evaEko/knife_whetting_level/docs/images/pcb_assembly/01-assembly_buttons.jpg

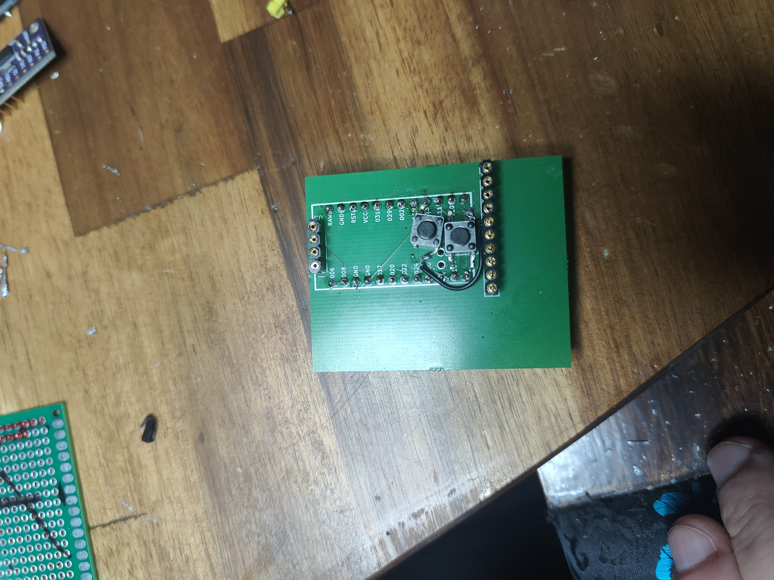
docs/images/pcb_assembly/01-assembly_buttons.jpg
