evaEko/knife_whetting_level/docs/images/pcb_assembly/02-assembly_display.jpg

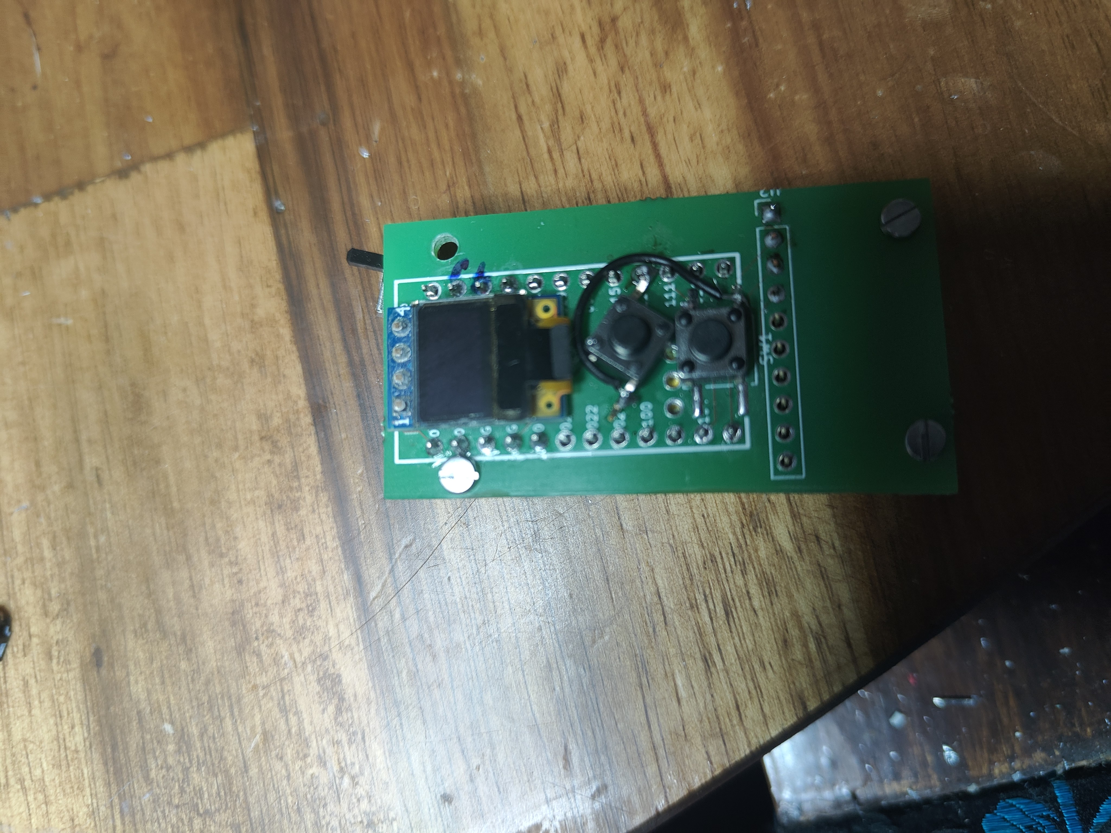
docs/images/pcb_assembly/02-assembly_display.jpg
