evaEko/knife_whetting_level/docs/images/pcb_assembly/03-assembly_adding_mcu.jpg

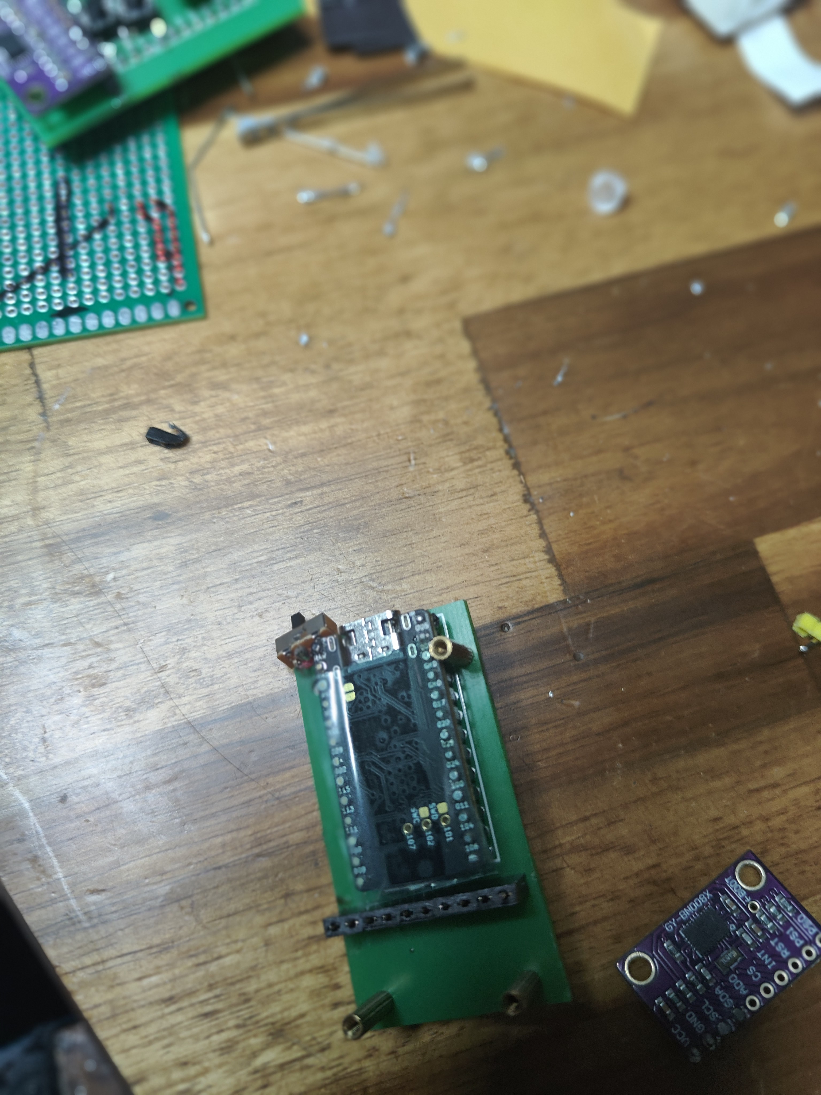
docs/images/pcb_assembly/03-assembly_adding_mcu.jpg
