evaEko/knife_whetting_level/docs/images/pcb_assembly/04-assembly_sensor_on_bottom.jpg

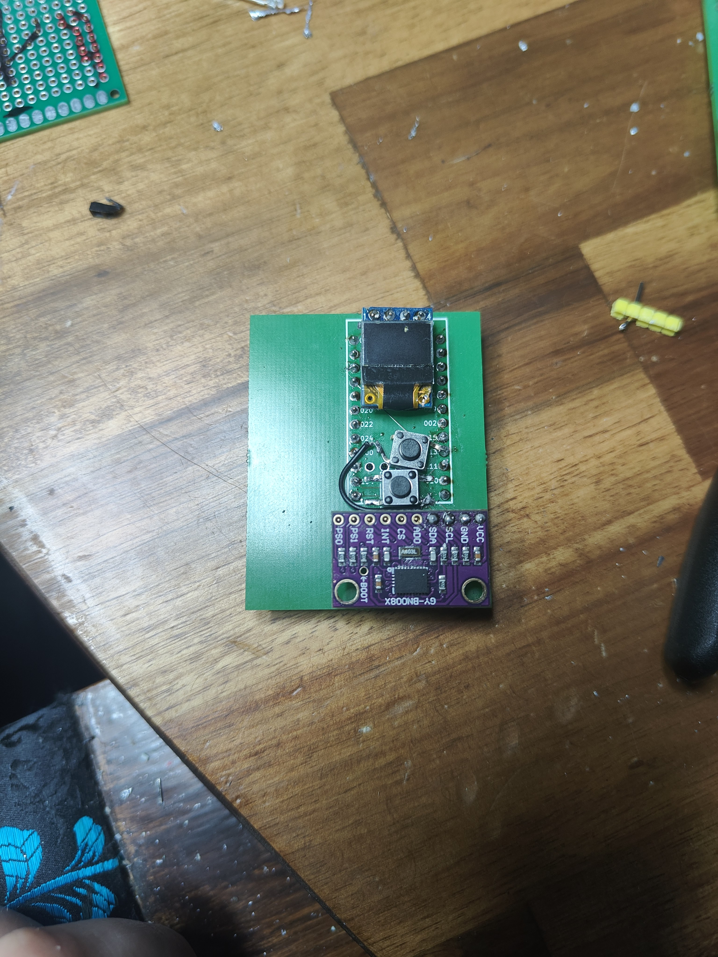
docs/images/pcb_assembly/04-assembly_sensor_on_bottom.jpg
