evaEko/knife_whetting_level/docs/images/pcb_assembly/04-assembly_sensor_on_top.jpg

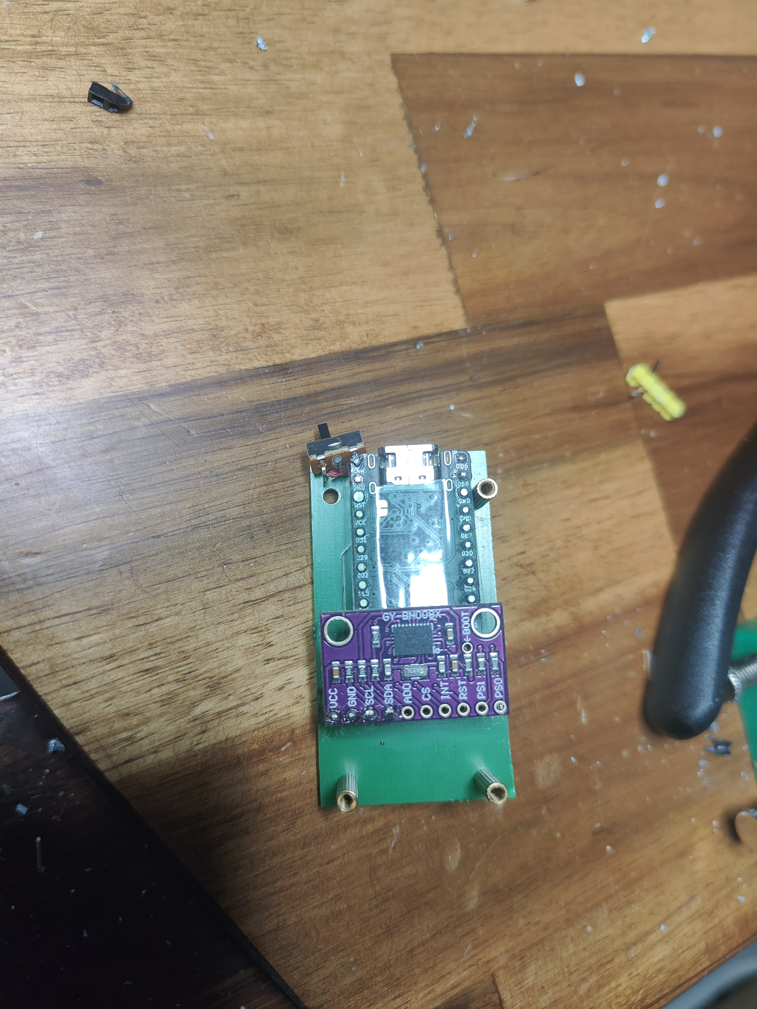
docs/images/pcb_assembly/04-assembly_sensor_on_top.jpg
